geissdoerfer/find/firmware/include/pt.h

#ifndef PT_H
#define PT_H

#include <stddef.h>

/* Protothread status values */
#define PT_STATUS_BLOCKED 0
#define PT_STATUS_FINISHED -1
#define PT_STATUS_YIELDED -2

/* Helper macros to generate unique labels */
#define _pt_line3(name, line) _pt_##name##line
#define _pt_line2(name, line) _pt_line3(name, line)
#define _pt_line(name) _pt_line2(name, __LINE__)

#if PT_USE_SETJMP
/*
 * Local continuation that uses setjmp()/longjmp() to keep thread state.
 *
 * Pros: local variables are preserved, works with all control structures.
 * Cons: slow, may erase global register variables.
 */
#include <setjmp.h>
struct pt
{
    jmp_buf env;
    int isset;
    int status;
};
#define pt_init()               \
    {                           \
        .isset = 0, .status = 0 \
    }
#define pt_begin(pt)               \
    do                             \
    {                              \
        if ((pt)->isset)           \
        {                          \
            longjmp((pt)->env, 0); \
        }                          \
    } while (0)
#define pt_label(pt, stat)     \
    do                         \
    {                          \
        (pt)->isset = 1;       \
        (pt)->status = (stat); \
        setjmp((pt)->env);     \
    } while (0)
#define pt_end(pt) pt_label(pt, PT_STATUS_FINISHED)
#elif PT_USE_GOTO
/*
 * Local continuation based on goto label references.
 *
 * Pros: works with all control sturctures.
 * Cons: requires GCC or Clang, doesn't preserve local variables.
 */
struct pt
{
    void *label;
    int status;
};
#define pt_init()                  \
    {                              \
        .label = NULL, .status = 0 \
    }
#define pt_begin(pt)             \
    do                           \
    {                            \
        if ((pt)->label != NULL) \
        {                        \
            goto *(pt)->label;   \
        }                        \
    } while (0)

#define pt_label(pt, stat)                                 \
    do                                                     \
    {                                                      \
        (pt)->status = (stat);                             \
        _pt_line(label) : (pt)->label = &&_pt_line(label); \
    } while (0)
#define pt_end(pt) pt_label(pt, PT_STATUS_FINISHED)
#else
/*
 * Local continuation based on switch/case and line numbers.
 *
 * Pros: works with any C99 compiler, most simple implementation.
 * Cons: doesn't allow more than one label per line, doesn't preserve local
 * variables.
 */
struct pt
{
    int label;
    int status;
};
#define pt_init()               \
    {                           \
        .label = 0, .status = 0 \
    }
#define pt_begin(pt)     \
    switch ((pt)->label) \
    {                    \
    case 0:
#define pt_label(pt, stat)      \
    do                          \
    {                           \
        (pt)->label = __LINE__; \
        (pt)->status = (stat);  \
    case __LINE__:;             \
    } while (0)
#define pt_end(pt)                    \
    pt_label(pt, PT_STATUS_FINISHED); \
    }
#endif

/*
 * Core protothreads API
 */
#define pt_status(pt) (pt)->status

#define pt_wait(pt, cond)                \
    do                                   \
    {                                    \
        pt_label(pt, PT_STATUS_BLOCKED); \
        if (!(cond))                     \
        {                                \
            return;                      \
        }                                \
    } while (0)

#define pt_yield(pt)                            \
    do                                          \
    {                                           \
        pt_label(pt, PT_STATUS_YIELDED);        \
        if (pt_status(pt) == PT_STATUS_YIELDED) \
        {                                       \
            (pt)->status = PT_STATUS_BLOCKED;   \
            return;                             \
        }                                       \
    } while (0)

#define pt_exit(pt, stat)   \
    do                      \
    {                       \
        pt_label(pt, stat); \
        return;             \
    } while (0)

#define pt_loop(pt, cond)                    \
    for (int _intr = 0; _intr == 0;)         \
        if (1)                               \
        {                                    \
            pt_label(pt, PT_STATUS_BLOCKED); \
            if (!(cond))                     \
            {                                \
                break;                       \
            }                                \
            goto _pt_line(body);             \
        }                                    \
        else                                 \
            while (1)                        \
                if (1)                       \
                {                            \
                    _intr = 1;               \
                    break;                   \
                }                            \
                else                         \
                    while (1)                \
                        if (1)               \
                        {                    \
                            return;          \
                        }                    \
                        else                 \
                            _pt_line(body) :

/*
 * Queues
 */
#define pt_queue(T, size) \
    struct                \
    {                     \
        T buf[size];      \
        unsigned int r;   \
        unsigned int w;   \
    }
#define pt_queue_init() \
    {                   \
        .r = 0, .w = 0  \
    }
#define pt_queue_len(q) (sizeof((q)->buf) / sizeof((q)->buf[0]))
#define pt_queue_cap(q) ((q)->w - (q)->r)
#define pt_queue_empty(q) ((q)->w == (q)->r)
#define pt_queue_full(q) (pt_queue_cap(q) == pt_queue_len(q))
#define pt_queue_reset(q) ((q)->w = (q)->r = 0)

#define pt_queue_push(q, el) \
    (!pt_queue_full(q) && ((q)->buf[(q)->w++ % pt_queue_len(q)] = (el), 1))
#define pt_queue_peek(q) \
    (pt_queue_empty(q) ? NULL : &(q)->buf[(q)->r % pt_queue_len(q)])
#define pt_queue_pop(q) \
    (pt_queue_empty(q) ? NULL : &(q)->buf[(q)->r++ % pt_queue_len(q)])

/*
 * Events
 */

#define pt_event() \
    struct         \
    {              \
        int s;     \
    }
#define pt_event_init() \
    {                   \
        .s = 0          \
    }
#define pt_event_get(e) (e)->s
#define pt_event_set(e) (e)->s = 1
#define pt_event_clear(e) (e)->s = 0
#define pt_event_wait(pt, e)  \
    pt_wait(pt, (e)->s == 1); \
    (e)->s = 0

#define pt_wait_hwevent(pt, evt) \
    evt = 0;                     \
    pt_wait(pt, evt == 1);       \
    evt = 0

/*
 * Wrapper for system calls and other functions that return -1 and set errno
 */
#define pt_sys(pt, call)                                                        \
    pt_wait(pt,                                                                 \
            (errno = 0) ||                                                      \
                !(((call) == -1) && (errno == EAGAIN || errno == EWOULDBLOCK || \
                                     errno == EINPROGRESS || errno == EINTR)))

typedef pt_event() pt_event_t;

#endif /* PT_H */
